ymic9963/69split/qmk/config.h

/* Copyright 2026 Yiannis Michael (ymich9963)

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
    You should have received a copy of the GNU General Public License
    along with this program. If not, see <https://www.gnu.org/licenses/>.
*/
#pragma once

#define MATRIX_ROWS 5
#define MATRIX_COLS 15
#define MATRIX_ROW_PINS { B1, B2, B3, B4, B5 }
#define MATRIX_COL_PINS { D4, D5, D6, D7, F5, F6, F7, NO_PIN, NO_PIN, NO_PIN, NO_PIN, NO_PIN, NO_PIN, NO_PIN, NO_PIN }
#define AUDIO_PIN B6
